jenul-ferdinand/unihack2026/esp32software/src/debug_config.h

#pragma once

// Master switch for all optional serial logging.
#define DEBUG_SERIAL_ENABLE 1

// Category-specific toggles. These are all disabled by default.
#define DEBUG_MAIN_STATE 0
#define DEBUG_DEAD_RECKONING 1
#define DEBUG_CLAMP_HOLD 0
#define DEBUG_IMU_ACCEL 0
#define DEBUG_GYRO_CLAMP 0
#define DEBUG_IMU_VERBOSE 0
#define DEBUG_PAIRING 0
#define DEBUG_BOOT_LOGS 0
